M4a1x/TPS5430/docs/led_drive.asc

D1: LED; NSSW008CT-P1
Q1: npn; 2N3904
R3: res; 10k
V1: voltage; PULSE(5.5 36 0 100u 100u)
V2: voltage; 1.221
Named nets: 0
.tran 0 100u 0
