M4a1x/TPS5430/docs/reverse_polarity_protection.asc

C2: cap; 4.7n
D1: zener; 1N750
M1: pmos; FDS6975
R1: res; 100k
R2: res; 12
V1: voltage; PULSE(-36 36 1 100n 100n 1 2)
Named nets: 0
.tran 0 {2+1u} {2-1u}
